ashishsinghchauhanfromtech/esp32-c3-wifi-tank-controller/images/28BYJ-48 -compact,-inexpensive-5V-4-phas-5-wire-unipolar-stepper-motor - Copy.jpeg

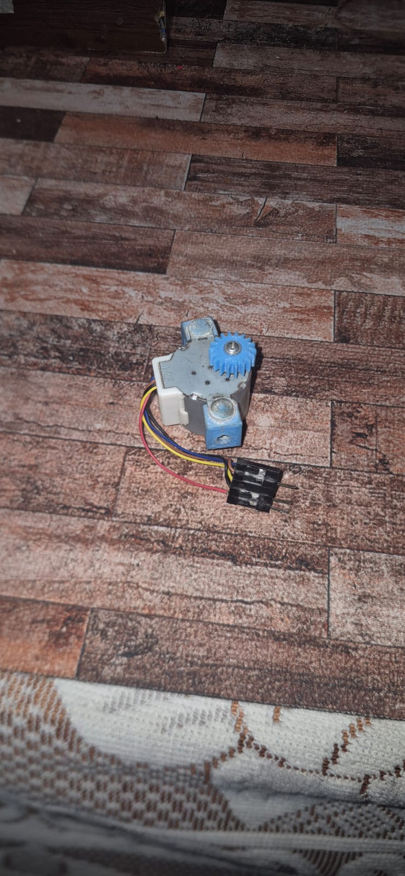
images/28BYJ-48 -compact,-inexpensive-5V-4-phas-5-wire-unipolar-stepper-motor - Copy.jpeg
