ashishsinghchauhanfromtech/esp32-c3-wifi-tank-controller/images/18650-Lithium-Ion-Charging-Module-Type-C- Copy.jpeg

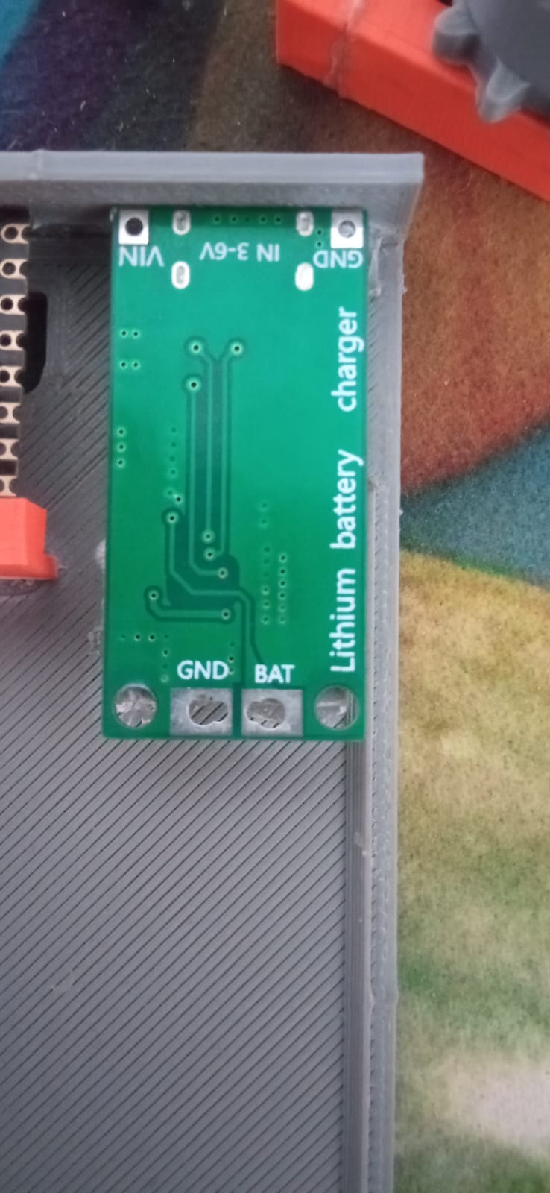
images/18650-Lithium-Ion-Charging-Module-Type-C- Copy.jpeg
