ashishsinghchauhanfromtech/esp32-c3-wifi-tank-controller/images/battery-pack-8.4v -Copy.jpeg

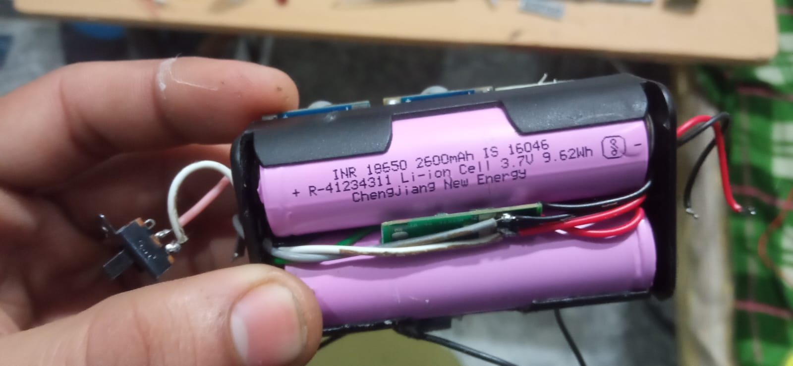
images/battery-pack-8.4v -Copy.jpeg
