ashishsinghchauhanfromtech/esp32-c3-wifi-tank-controller/images/battery-pack-with-BMS-Copy.jpeg

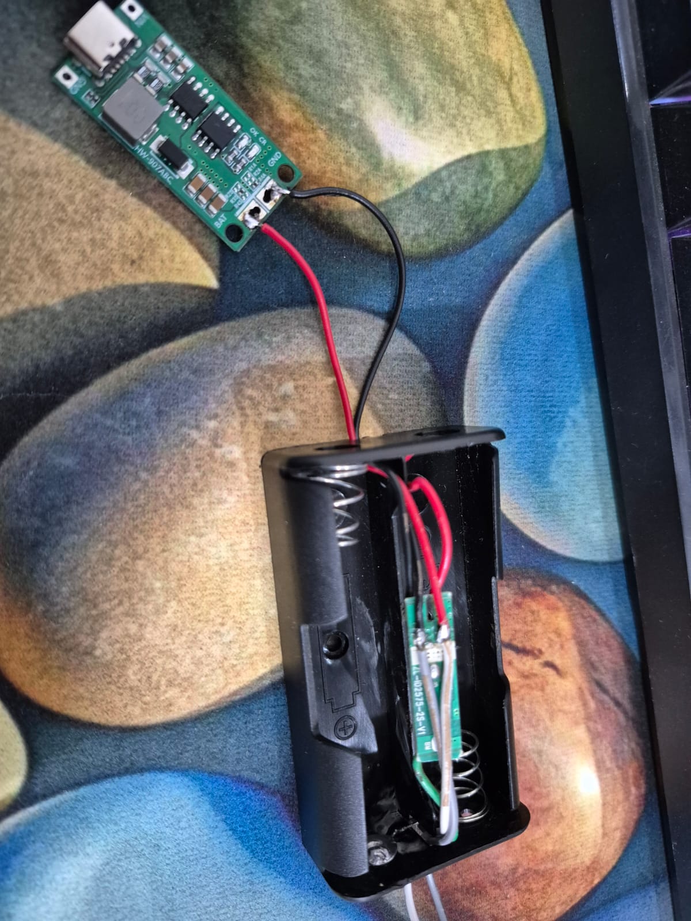
images/battery-pack-with-BMS-Copy.jpeg
