ashishsinghchauhanfromtech/esp32-c3-wifi-tank-controller/images/belt-prototype-1.jpeg

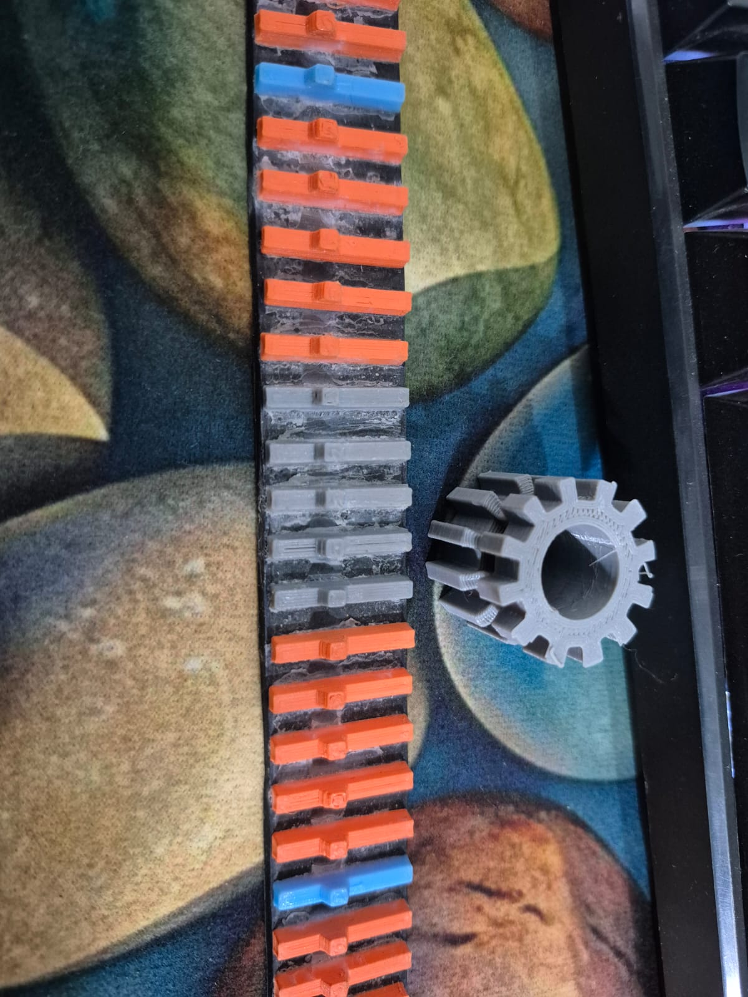
images/belt-prototype-1.jpeg
