ashishsinghchauhanfromtech/esp32-c3-wifi-tank-controller/images/Diagram-of-base-Copy.jpeg

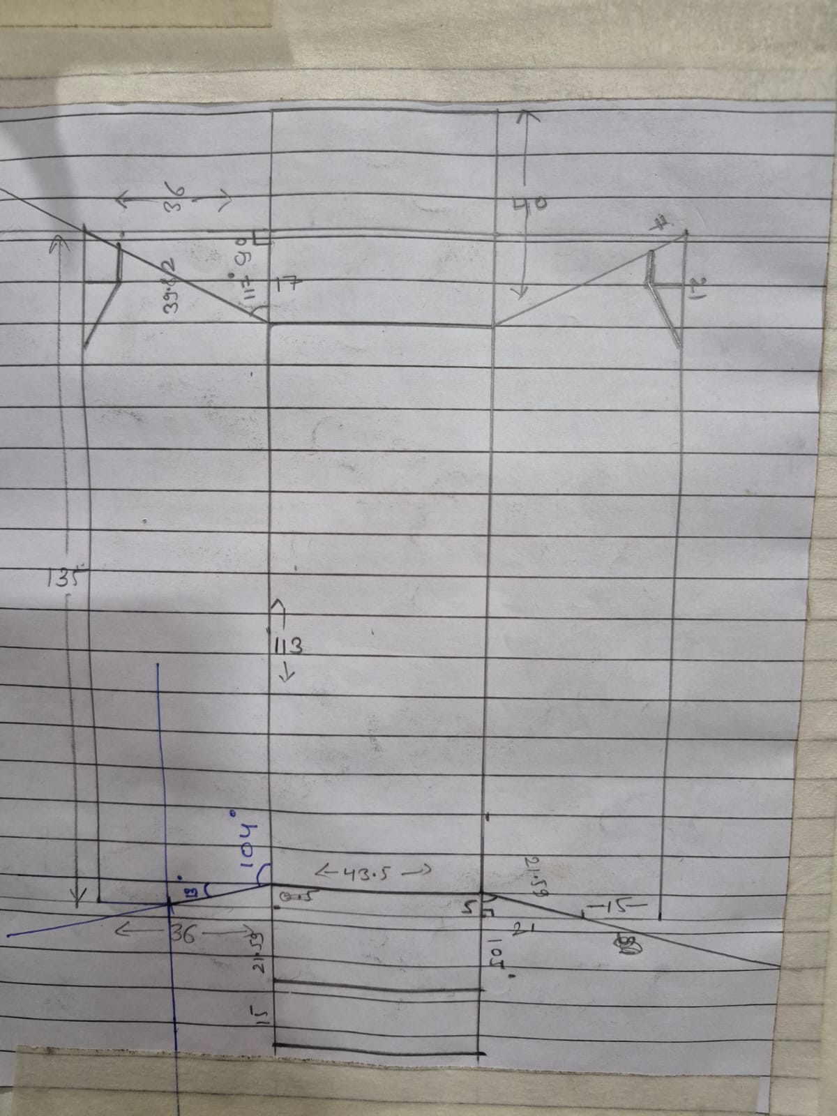
images/Diagram-of-base-Copy.jpeg
