ashishsinghchauhanfromtech/esp32-c3-wifi-tank-controller/images/diagram-of-base-locating-led-and-wifi-Copy.jpeg

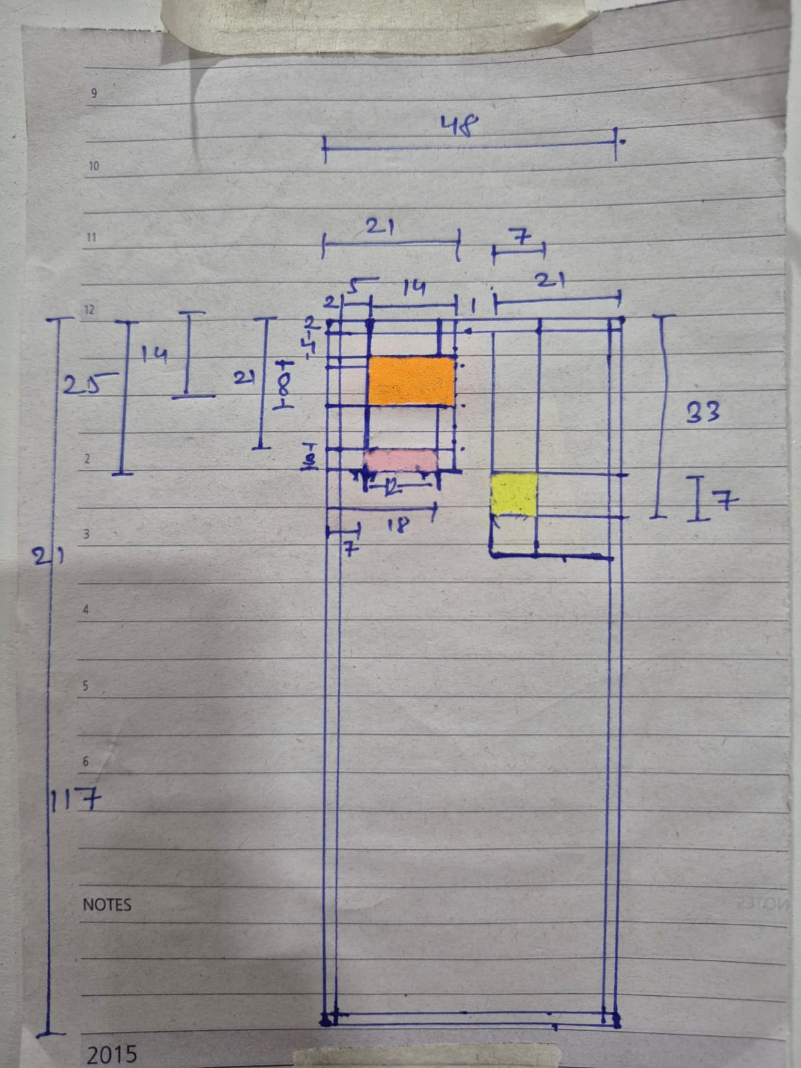
images/diagram-of-base-locating-led-and-wifi-Copy.jpeg
