ashishsinghchauhanfromtech/esp32-c3-wifi-tank-controller/images/diagram-of-basic-side-Copy.jpeg

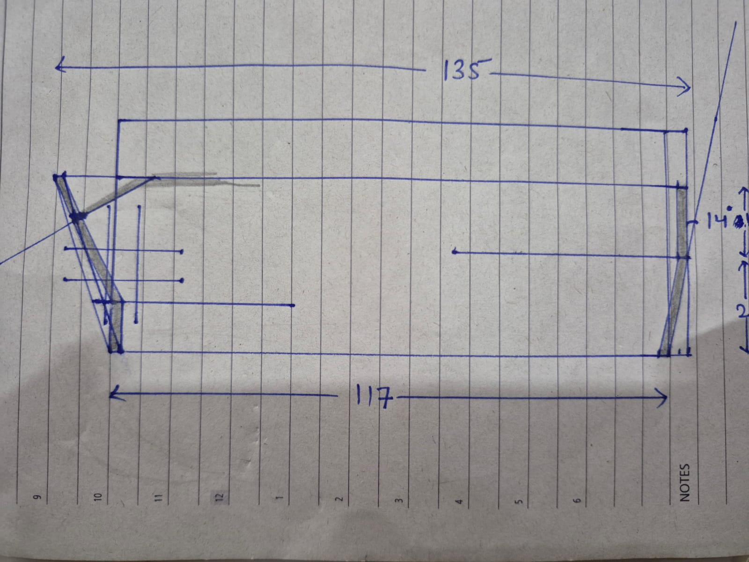
images/diagram-of-basic-side-Copy.jpeg
