ashishsinghchauhanfromtech/esp32-c3-wifi-tank-controller/images/diagram-of-side-profile-2-Copy.jpeg

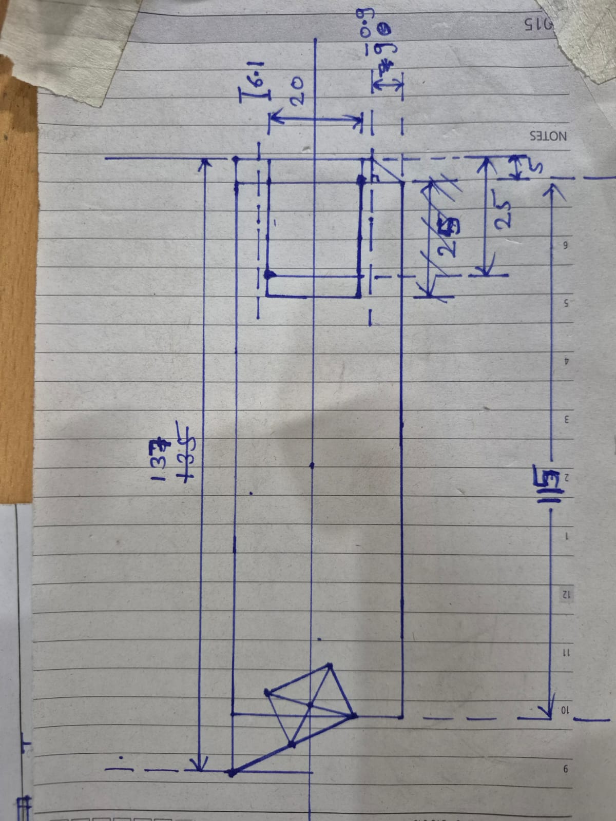
images/diagram-of-side-profile-2-Copy.jpeg
