ashishsinghchauhanfromtech/esp32-c3-wifi-tank-controller/images/diagram-of-side-profile-Copy.jpeg

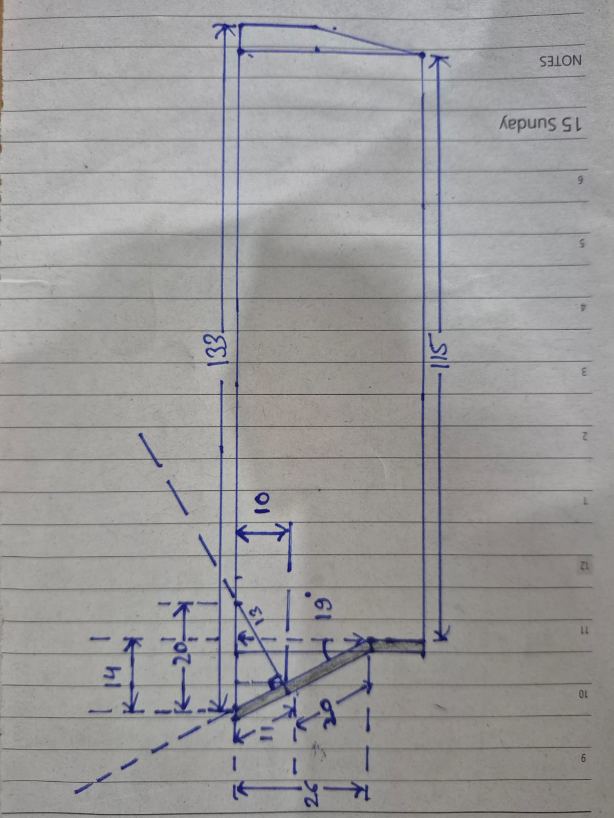
images/diagram-of-side-profile-Copy.jpeg
