ashishsinghchauhanfromtech/esp32-c3-wifi-tank-controller/images/esp32-c3-MicroControler-Copy.jpeg

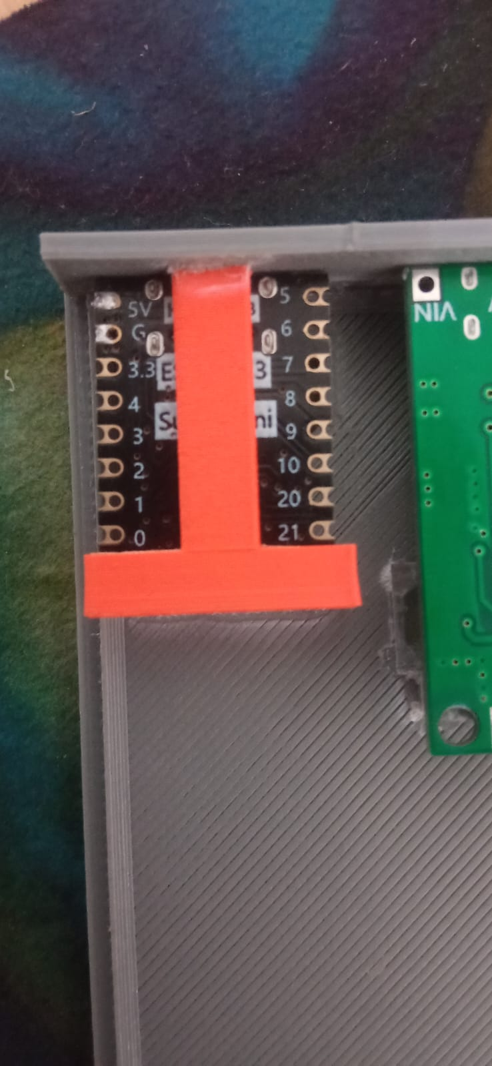
images/esp32-c3-MicroControler-Copy.jpeg
