ashishsinghchauhanfromtech/esp32-c3-wifi-tank-controller/images/esp-chargingmodule-battery-pac-and-MPU.jpeg

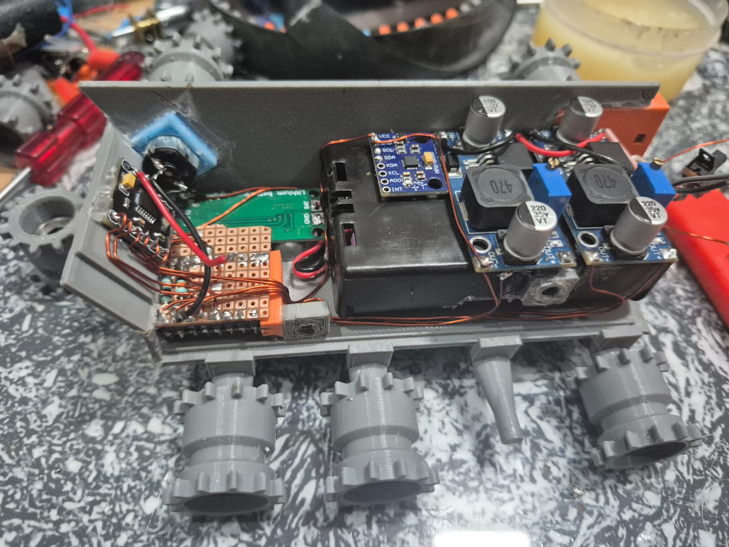
images/esp-chargingmodule-battery-pac-and-MPU.jpeg
