ashishsinghchauhanfromtech/esp32-c3-wifi-tank-controller/images/esp-with-charging-module-Copy.jpeg

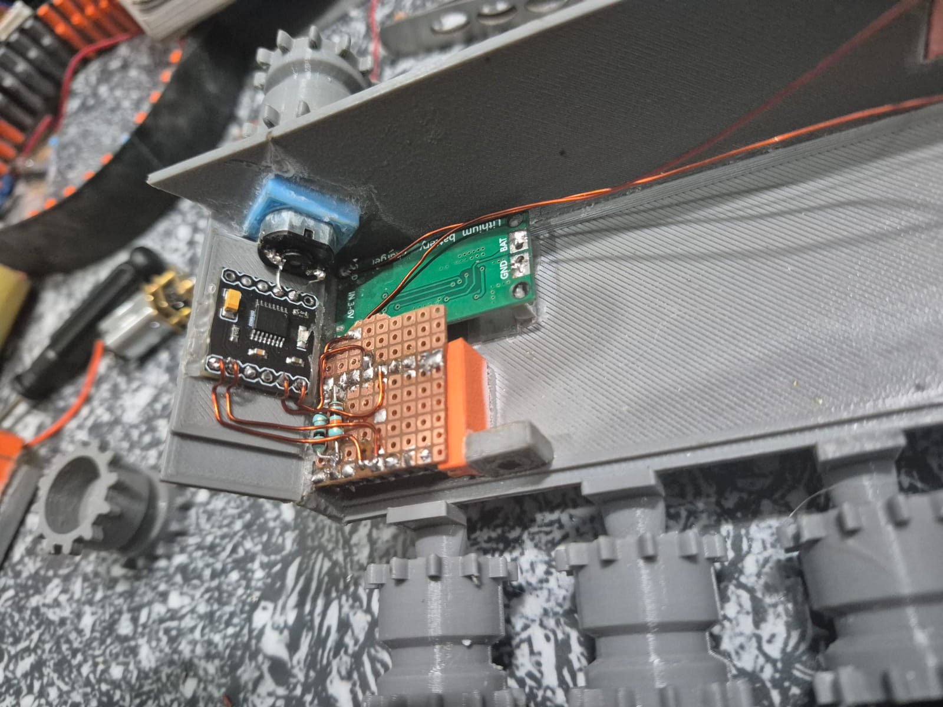
images/esp-with-charging-module-Copy.jpeg
