ashishsinghchauhanfromtech/esp32-c3-wifi-tank-controller/images/prototype-a1.jpeg

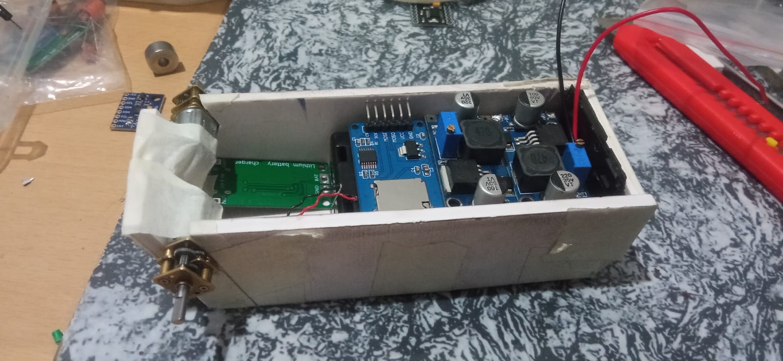
images/prototype-a1.jpeg
