ashishsinghchauhanfromtech/esp32-c3-wifi-tank-controller/images/prototype-a2.jpeg

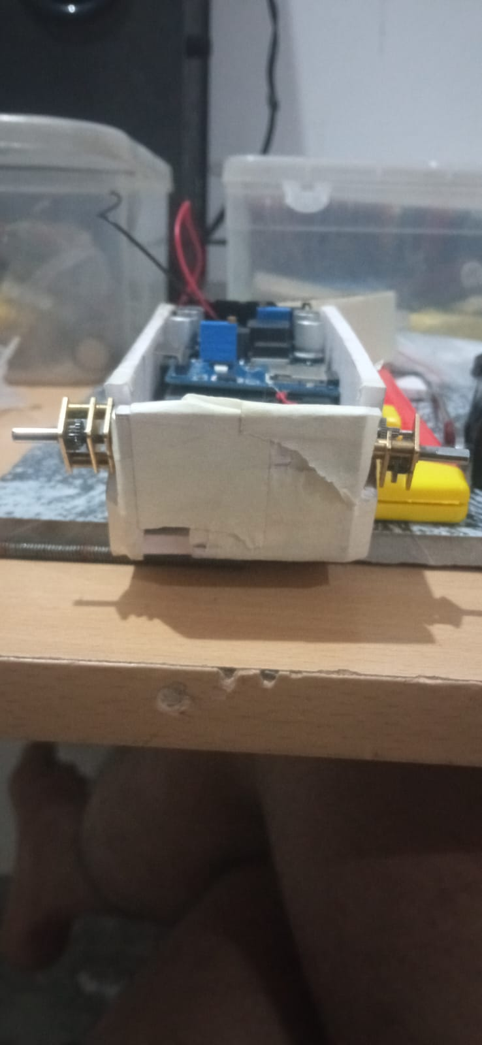
images/prototype-a2.jpeg
