ashishsinghchauhanfromtech/esp32-c3-wifi-tank-controller/images/prototype-a3.jpeg

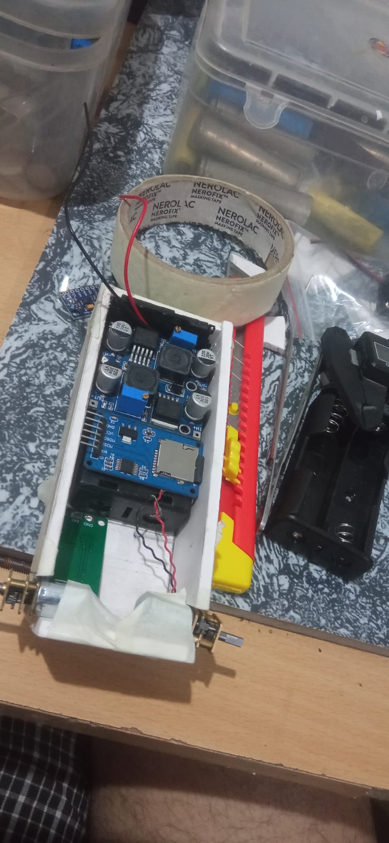
images/prototype-a3.jpeg
