ashishsinghchauhanfromtech/esp32-c3-wifi-tank-controller/images/prototype-b2-Copy.jpeg

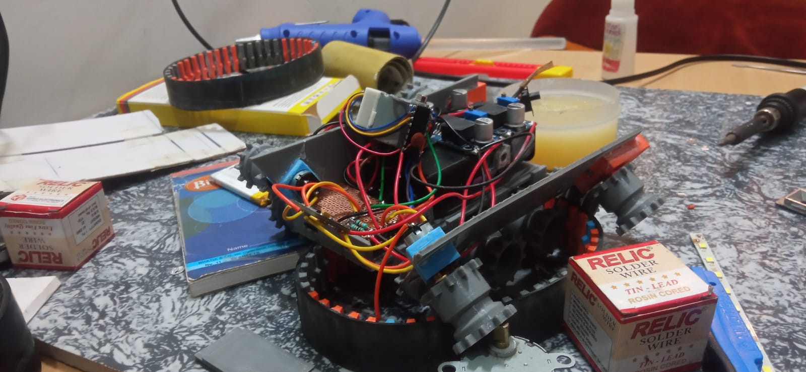
images/prototype-b2-Copy.jpeg
