ashishsinghchauhanfromtech/esp32-c3-wifi-tank-controller/images/prototype-d1-Copy.jpeg

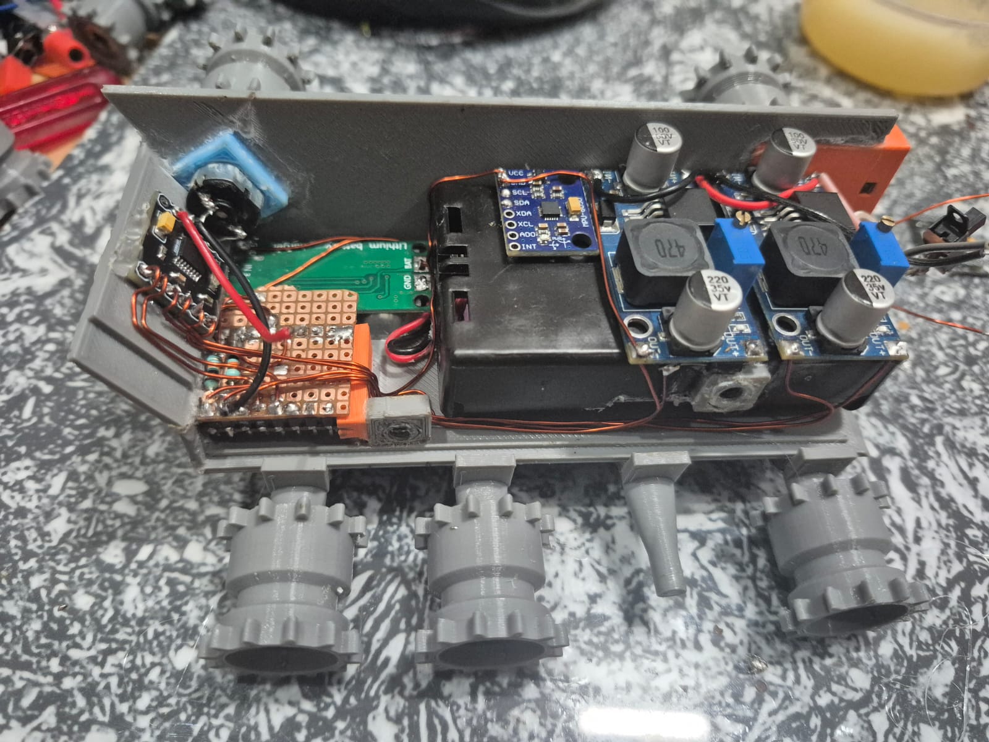
images/prototype-d1-Copy.jpeg
