ashishsinghchauhanfromtech/esp32-c3-wifi-tank-controller/images/Prototype-d4-Copy.jpeg

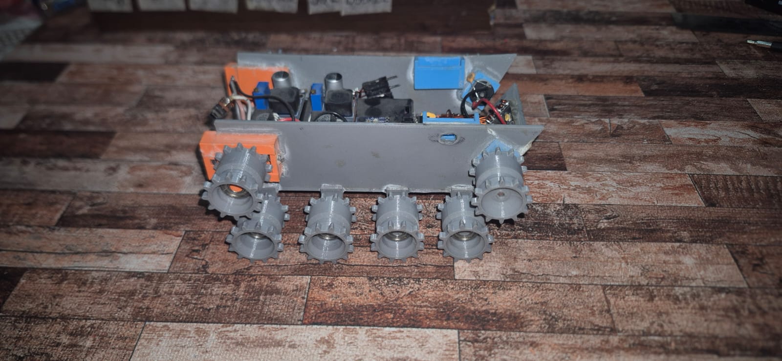
images/Prototype-d4-Copy.jpeg
