ashishsinghchauhanfromtech/esp32-c3-wifi-tank-controller/images/Prototype-d5-Copy.jpeg

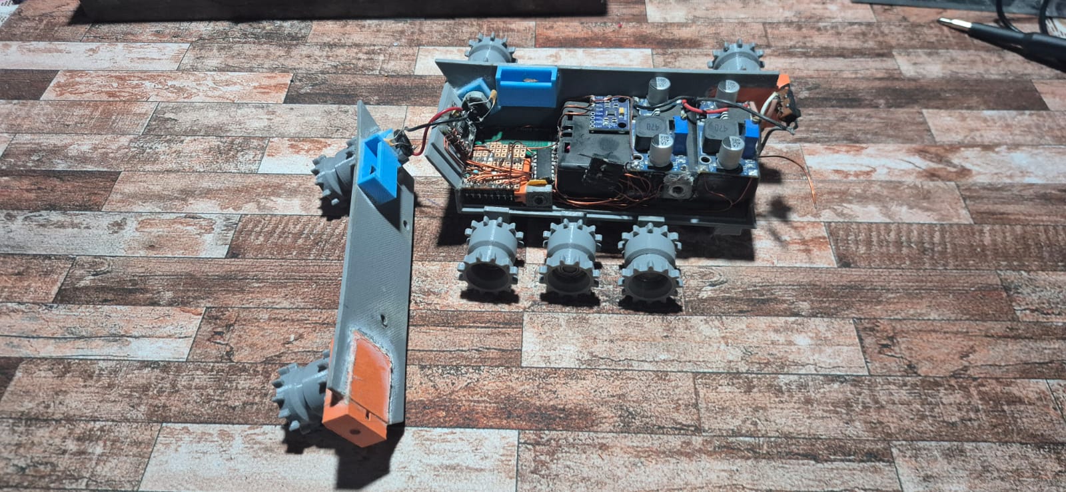
images/Prototype-d5-Copy.jpeg
