ashishsinghchauhanfromtech/esp32-c3-wifi-tank-controller/images/Prototype-d7-Copy.jpeg

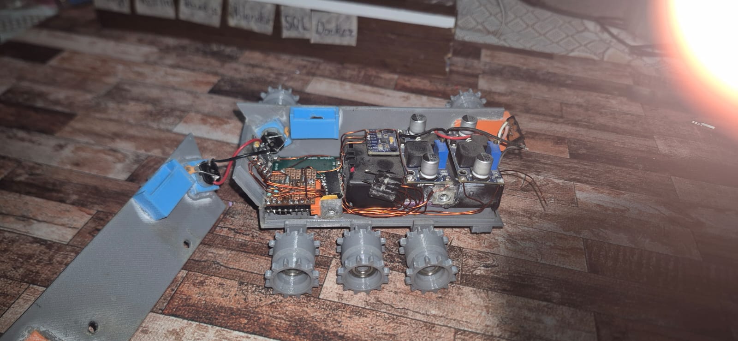
images/Prototype-d7-Copy.jpeg
