ashishsinghchauhanfromtech/esp32-c3-wifi-tank-controller/images/Prototype-d8-Copy.jpeg

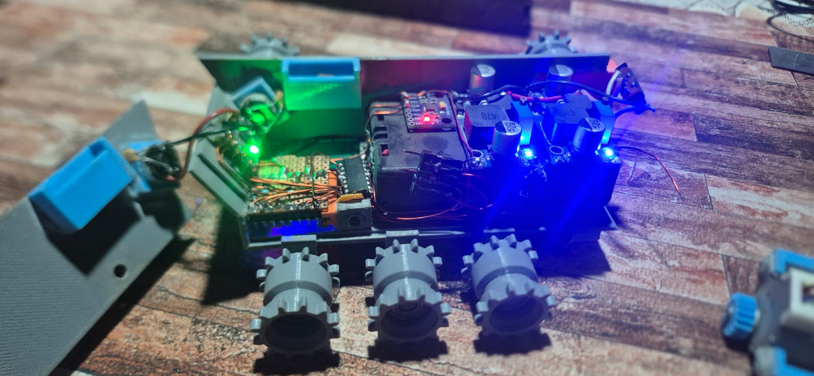
images/Prototype-d8-Copy.jpeg
