ashishsinghchauhanfromtech/esp32-c3-wifi-tank-controller/images/tank-belt-connector.jpeg

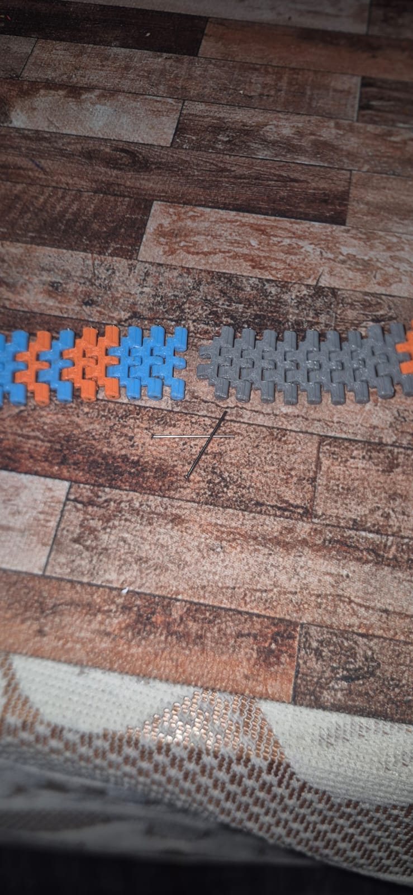
images/tank-belt-connector.jpeg
