ashishsinghchauhanfromtech/esp32-c3-wifi-tank-controller/images/Tank-e2-Copy.jpeg

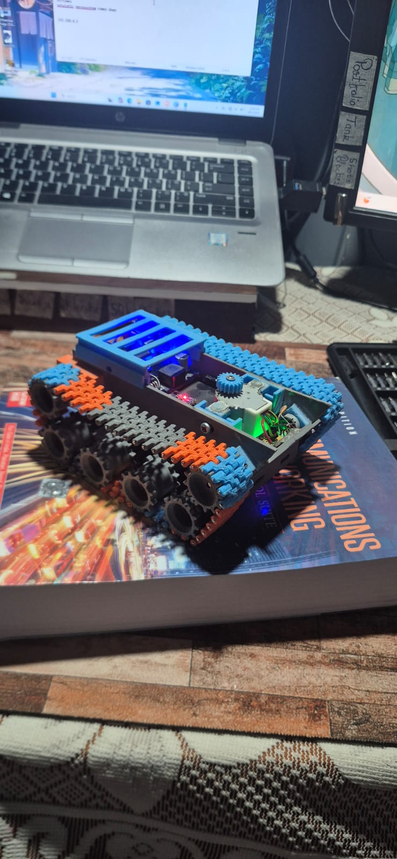
images/Tank-e2-Copy.jpeg
