ashishsinghchauhanfromtech/esp32-c3-wifi-tank-controller/images/Tank-e3-bottom.jpeg

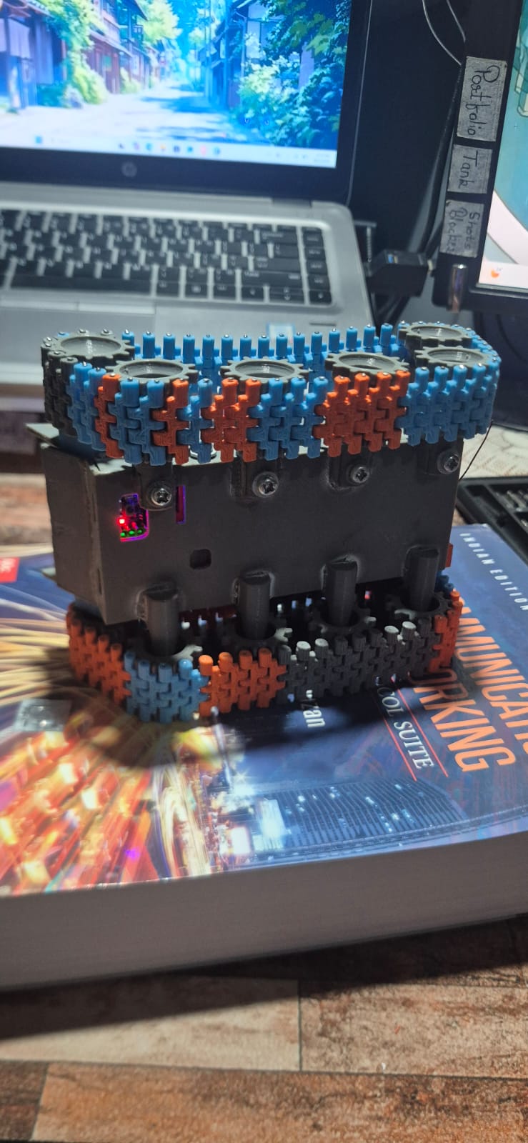
images/Tank-e3-bottom.jpeg
