ashishsinghchauhanfromtech/esp32-c3-wifi-tank-controller/images/Tank-e5.jpeg

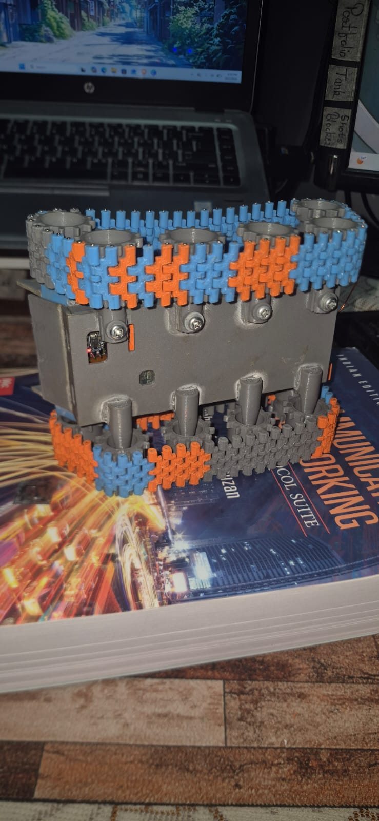
images/Tank-e5.jpeg
