ashishsinghchauhanfromtech/esp32-c3-wifi-tank-controller/images/Tank-e6-front-Copy.jpeg

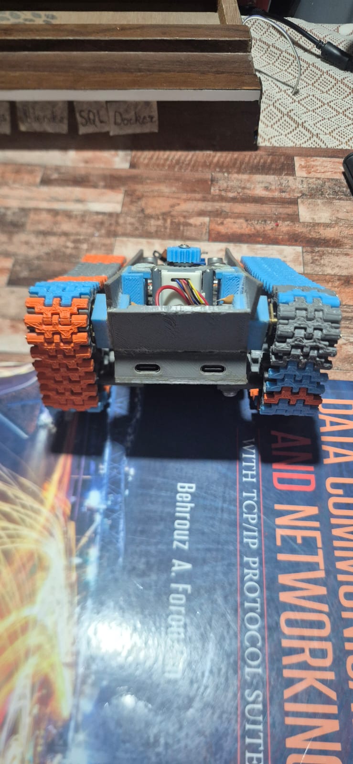
images/Tank-e6-front-Copy.jpeg
