ashishsinghchauhanfromtech/esp32-c3-wifi-tank-controller/images/Tank-e7-side.jpeg

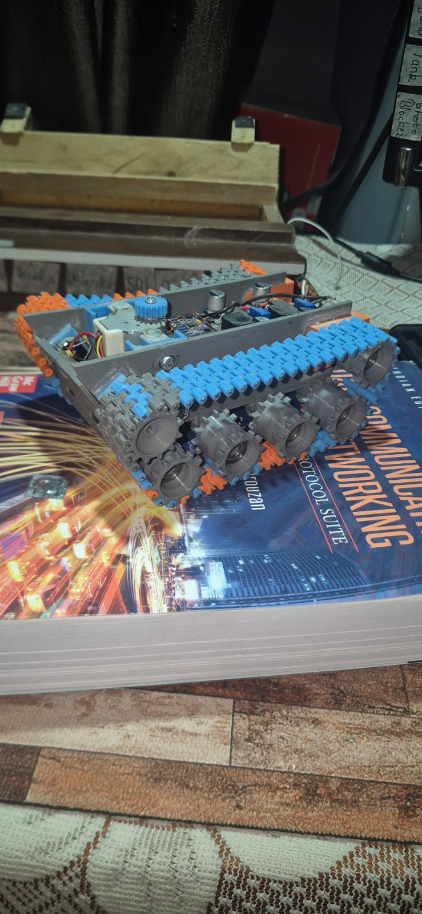
images/Tank-e7-side.jpeg
