ashishsinghchauhanfromtech/esp32-c3-wifi-tank-controller/images/tank-progress-2-Copy.jpeg

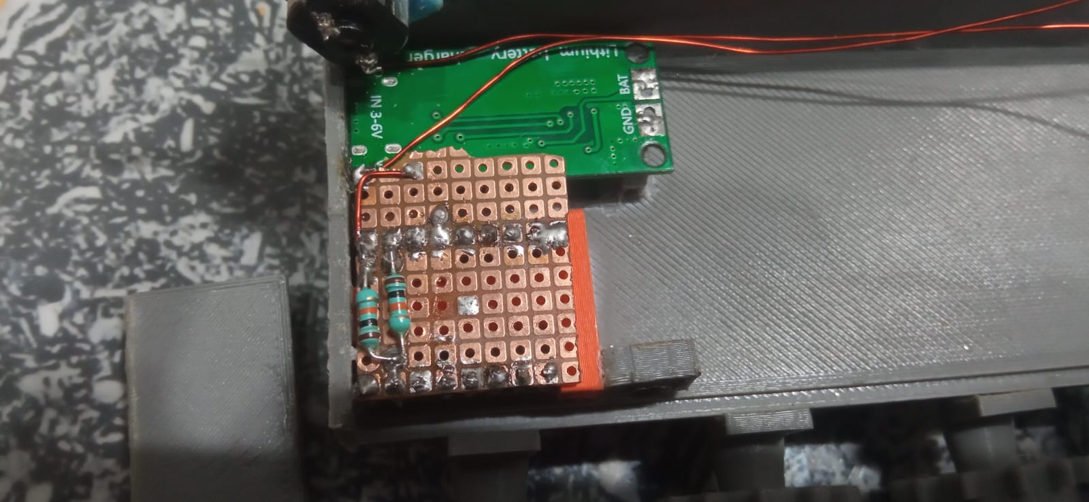
images/tank-progress-2-Copy.jpeg
