ashishsinghchauhanfromtech/esp32-c3-wifi-tank-controller/images/tank-top-part.jpeg

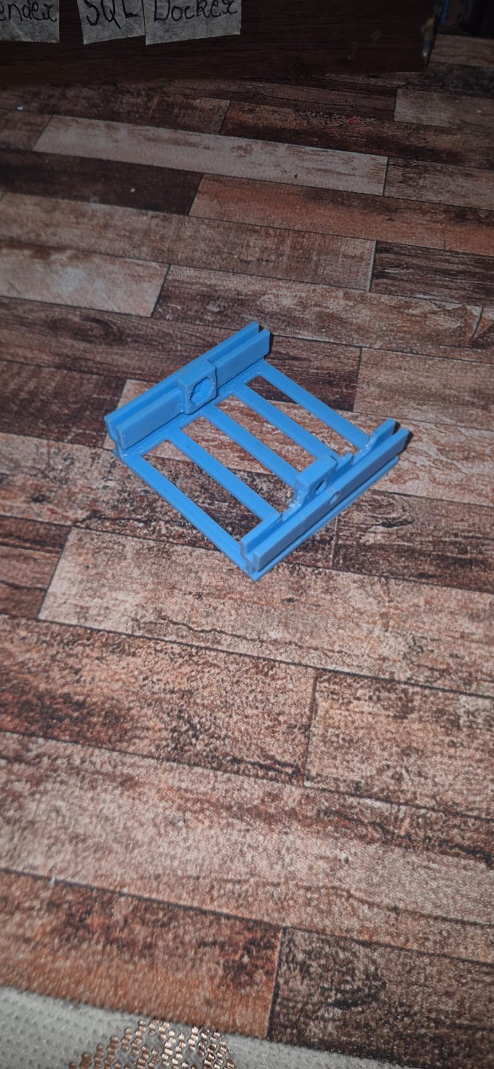
images/tank-top-part.jpeg
