ashishsinghchauhanfromtech/esp32-c3-wifi-tank-controller/images/ULN-Copy.jpeg

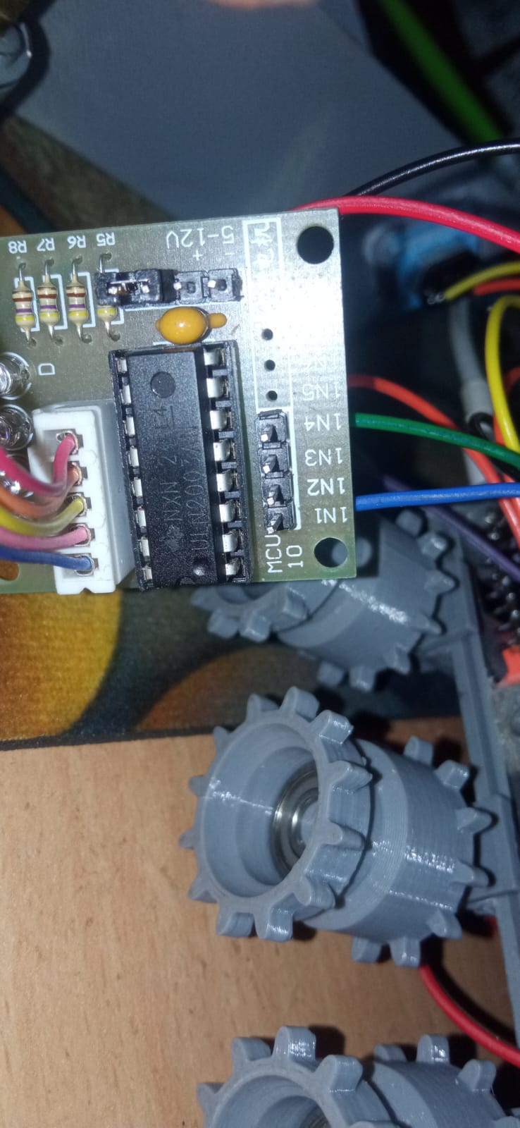
images/ULN-Copy.jpeg
