ashishsinghchauhanfromtech/esp32-c3-wifi-tank-controller/images/unl-color-grading-Copy.jpeg

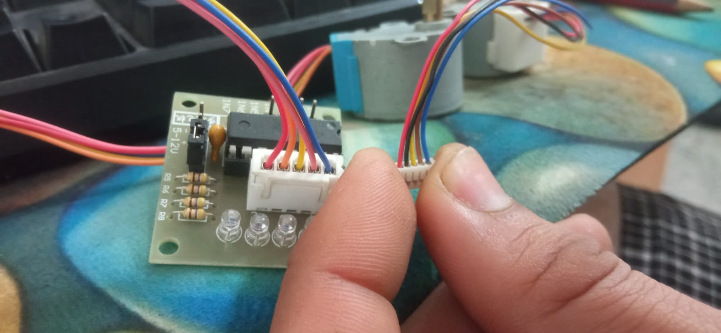
images/unl-color-grading-Copy.jpeg
