ashishsinghchauhanfromtech/esp32-c3-wifi-tank-controller/images/wheel-mount.jpeg

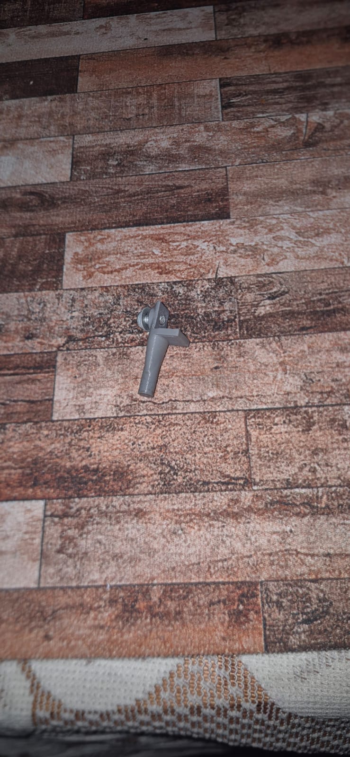
images/wheel-mount.jpeg
