ashishsinghchauhanfromtech/esp32-c3-wifi-tank-controller/tank controller/controller image which is uploaded in the esp itself using littlefs.jpeg

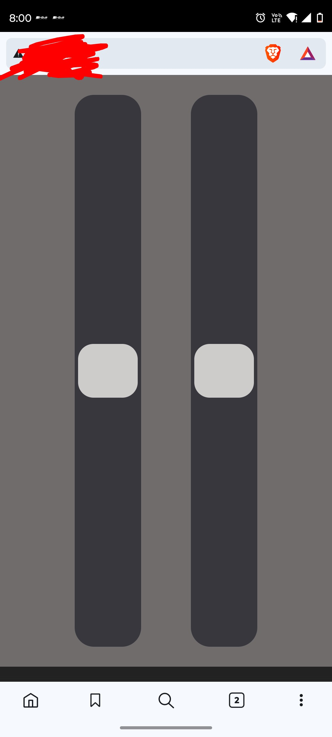
tank controller/controller image which is uploaded in the esp itself using littlefs.jpeg
