ashishsinghchauhanfromtech/esp32-c3-wifi-tank-controller/mechanical-design/tank-nozel-motor-top-mount.stl

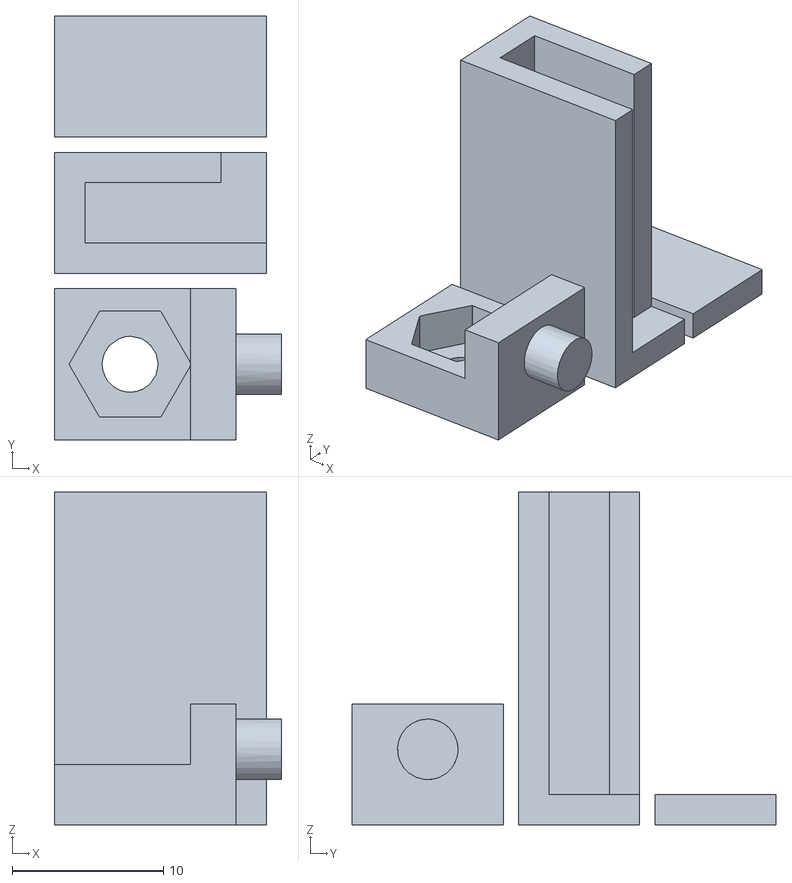
[picture p63: CAD file, 2026-10-01]
mechanical-design/tank-nozel-motor-top-mount.stl
15.0 x 28.0 x 22.0
