ashishsinghchauhanfromtech/esp32-c3-wifi-tank-controller/mechanical-design/Chassis-Base-parallel-to-ground-with-usb-and-charging-indicator.stl

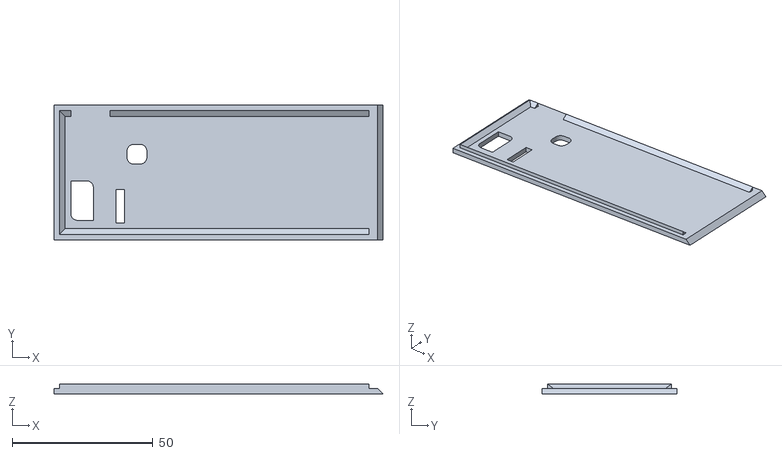
[picture p64: CAD file, 2026-10-01]
mechanical-design/Chassis-Base-parallel-to-ground-with-usb-and-charging-indicator.stl
117.0 x 48.0 x 3.50
