ashishsinghchauhanfromtech/esp32-c3-wifi-tank-controller/mechanical-design/esp32-c3-mount.stl

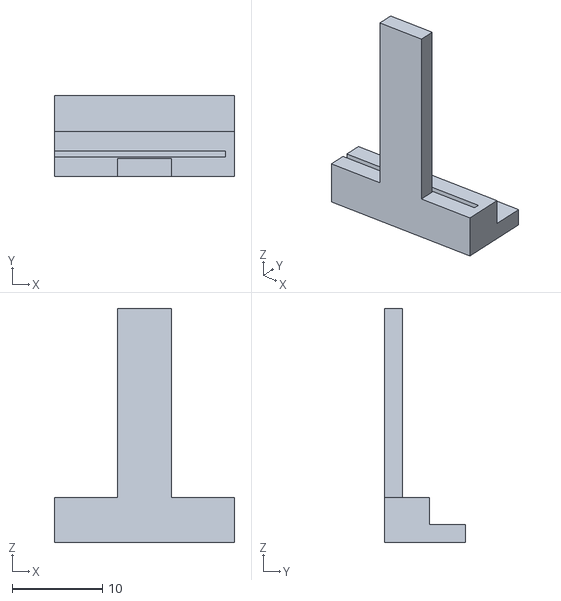
[picture p65: CAD file, 2026-10-01]
mechanical-design/esp32-c3-mount.stl
20.0 x 9.00 x 26.0
