ashishsinghchauhanfromtech/esp32-c3-wifi-tank-controller/mechanical-design/Chassis-side-profile-for-belttightningwheels-groundwheels-enginewheels.stl

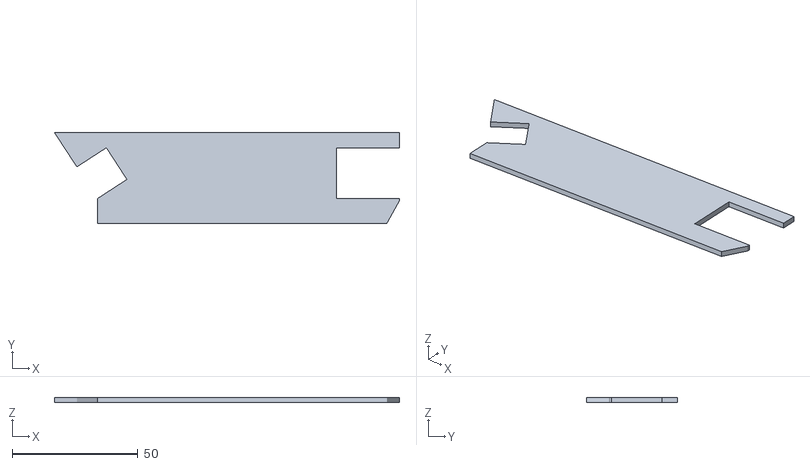
[picture p66: CAD file, 2026-10-01]
mechanical-design/Chassis-side-profile-for-belttightningwheels-groundwheels-enginewheels.stl
137.0 x 36.0 x 2.00
