ashishsinghchauhanfromtech/esp32-c3-wifi-tank-controller/mechanical-design/Tank-nozel-motor-mount-on-top.stl

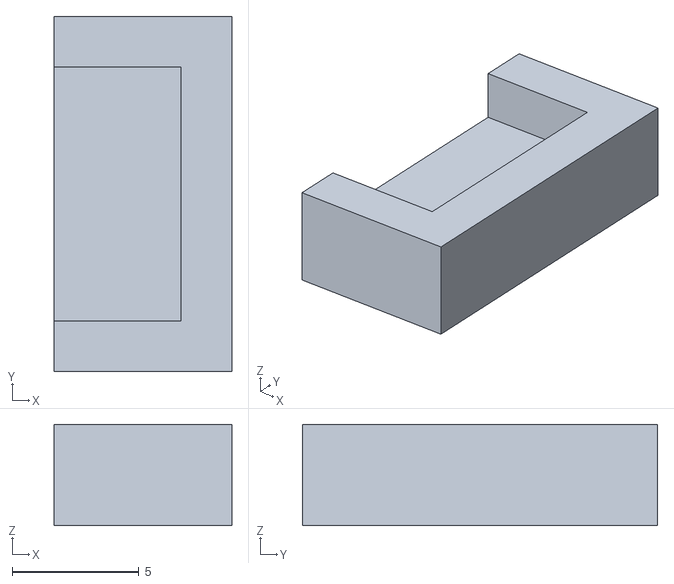
[picture p67: CAD file, 2026-10-01]
mechanical-design/Tank-nozel-motor-mount-on-top.stl
7.00 x 14.0 x 4.00
