ashishsinghchauhanfromtech/esp32-c3-wifi-tank-controller/images/3d-printing-of-wheel-5.jpeg

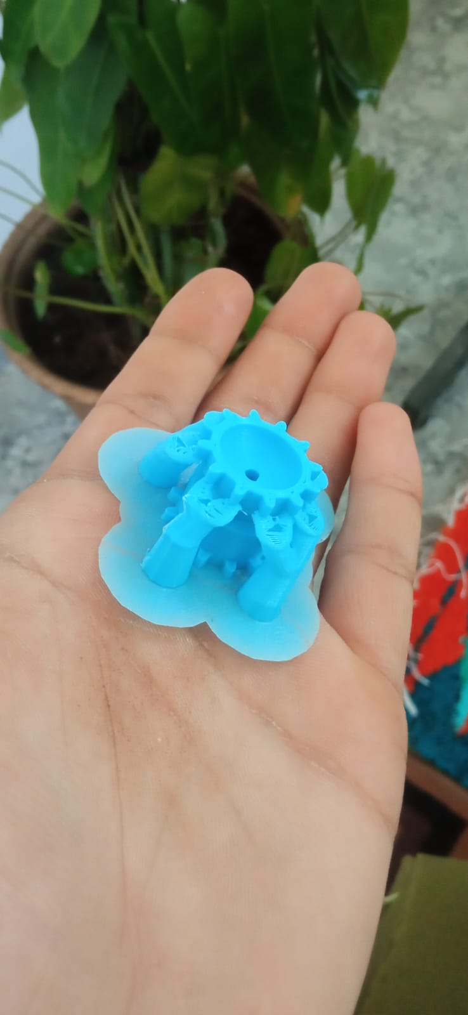
images/3d-printing-of-wheel-5.jpeg
