ashishsinghchauhanfromtech/esp32-c3-wifi-tank-controller/images/printed-base.jpeg

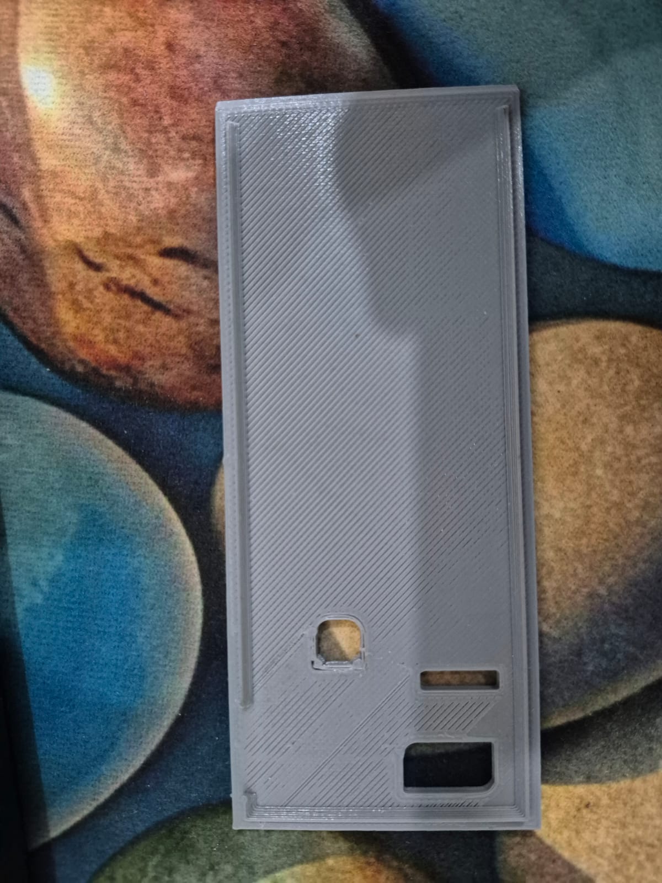
images/printed-base.jpeg
