ashishsinghchauhanfromtech/esp32-c3-wifi-tank-controller/images/Printed-side-part.jpeg

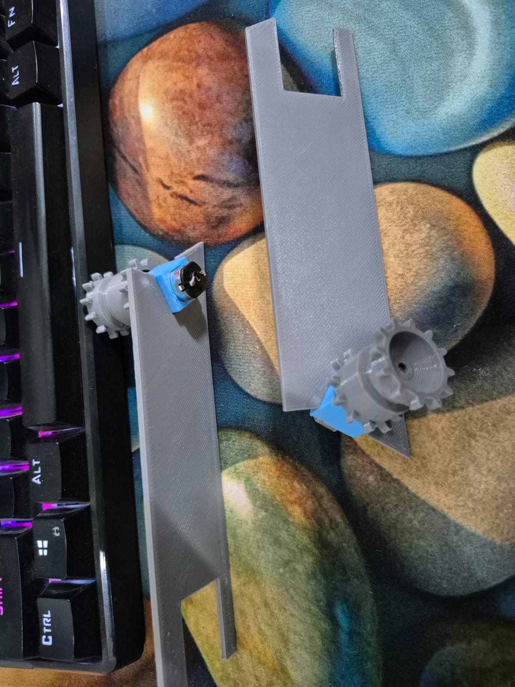
images/Printed-side-part.jpeg
